mahmoud-elghamry/thermocouple/docs/reference/benchmarks/murphy-tdxm/photo-1.jpg

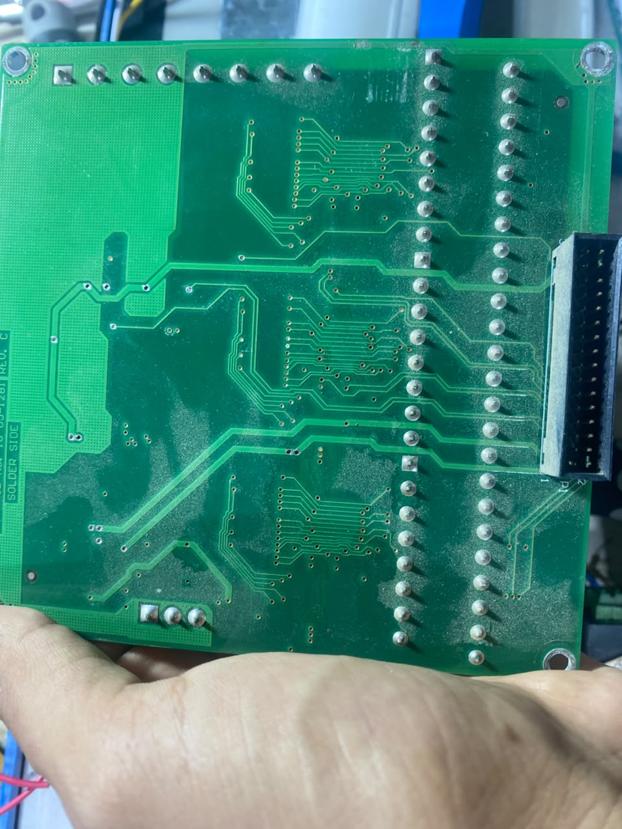
docs/reference/benchmarks/murphy-tdxm/photo-1.jpg
