mahmoud-elghamry/thermocouple/docs/reference/benchmarks/murphy-tdxm/photo-2.jpg

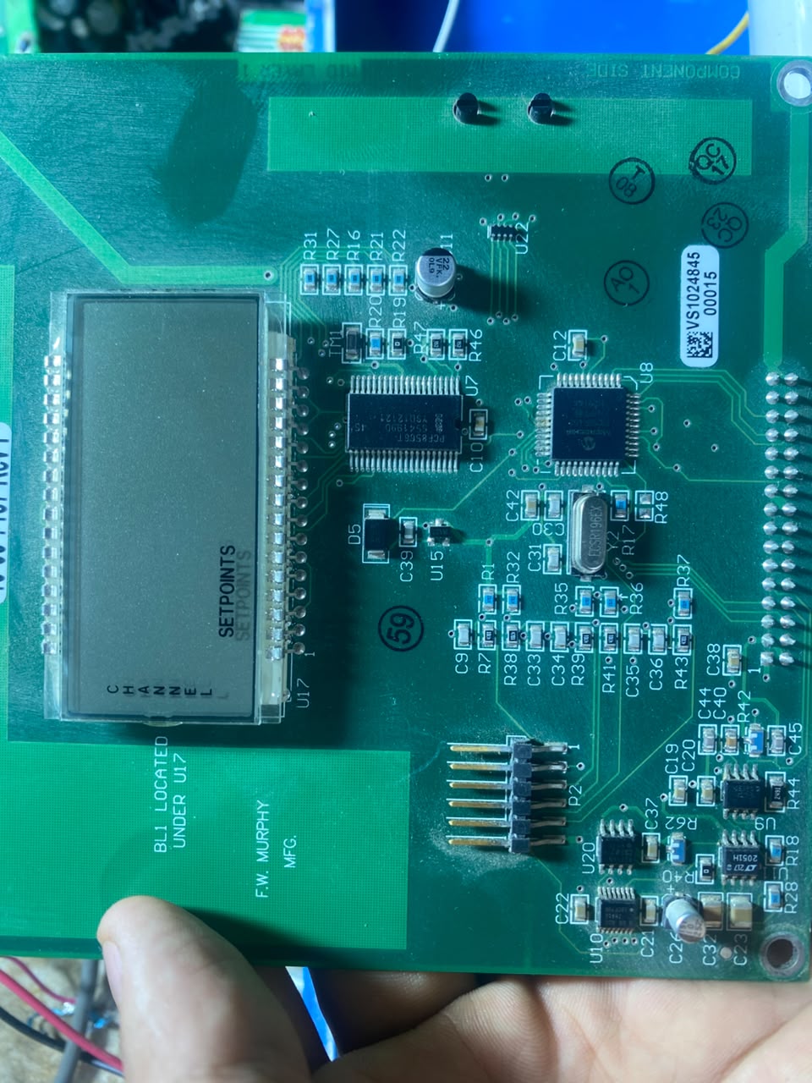
docs/reference/benchmarks/murphy-tdxm/photo-2.jpg
