mahmoud-elghamry/thermocouple/docs/reference/benchmarks/murphy-tdxm/photo-3.jpg

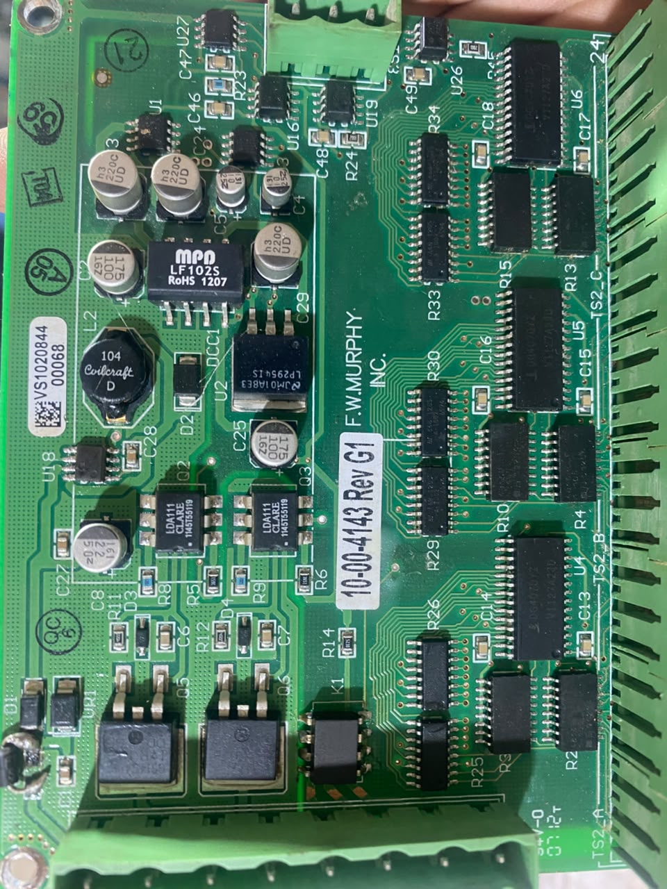
docs/reference/benchmarks/murphy-tdxm/photo-3.jpg
