mahmoud-elghamry/thermocouple/docs/reference/benchmarks/murphy-tdxm/photo-4.jpg

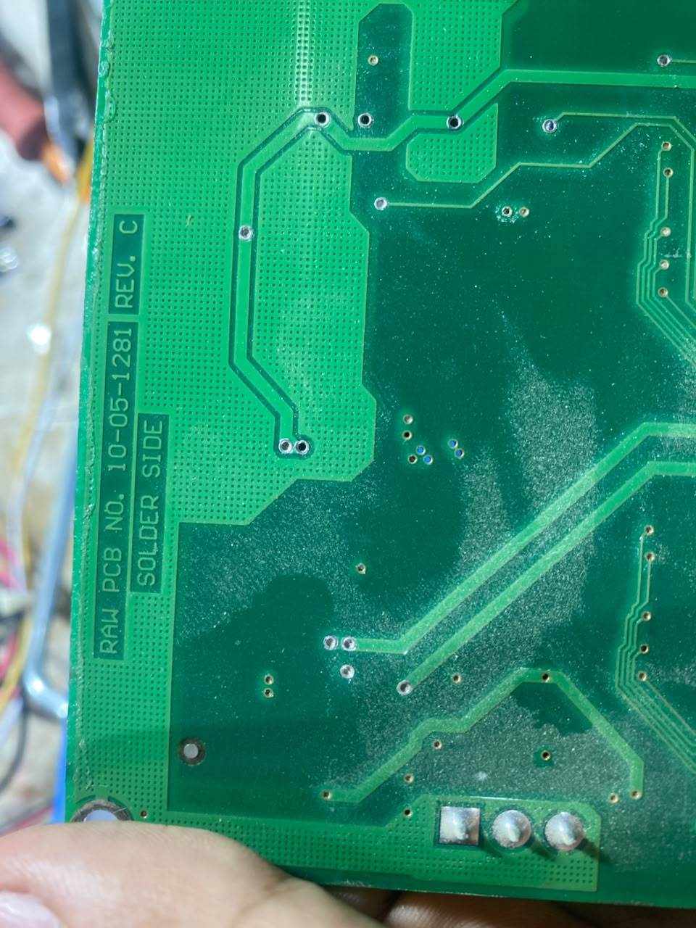
docs/reference/benchmarks/murphy-tdxm/photo-4.jpg
