mahmoud-elghamry/thermocouple/docs/reference/benchmarks/murphy-tdxm/photo-5.jpg

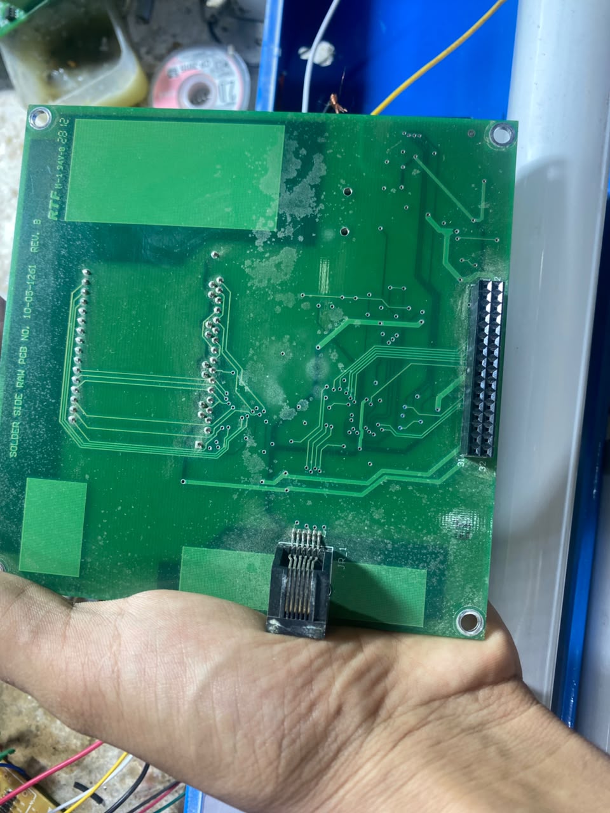
docs/reference/benchmarks/murphy-tdxm/photo-5.jpg
