mahmoud-elghamry/thermocouple/docs/reference/benchmarks/murphy-tdxm/photo-8.jpg

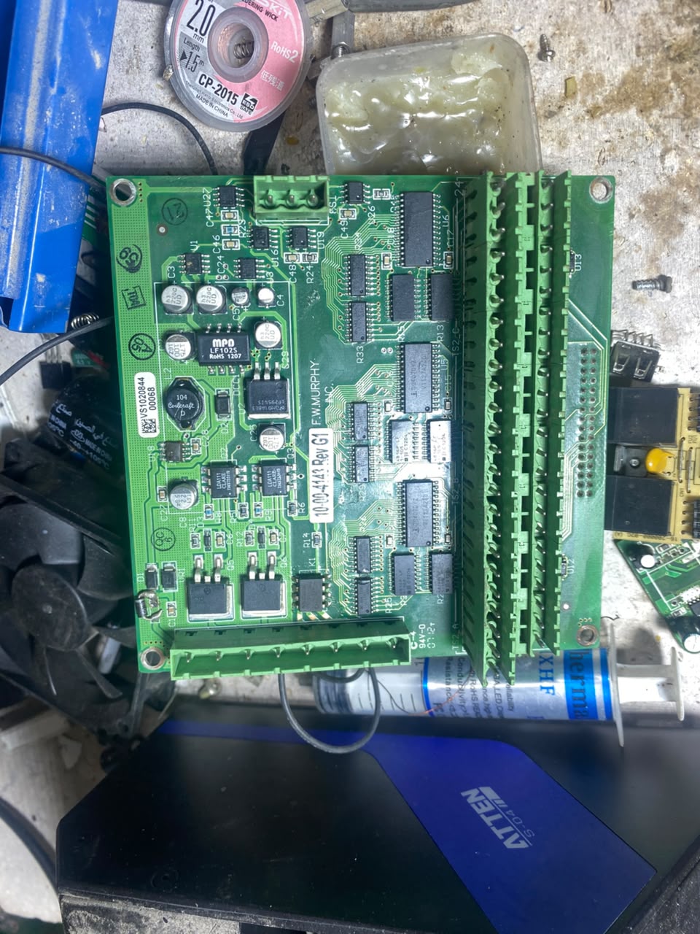
docs/reference/benchmarks/murphy-tdxm/photo-8.jpg
