mahmoud-elghamry/thermocouple/hardware/24ch/gen/finish.py

"""Incremental finishing of the routed board - never moves a footprint.

Works on ../thermo24.kicad_pcb after a routing result was kept (docs/TOOLS.md,
"24-channel board"). Run with KiCad's python:
    python finish.py drc                 # KiCad DRC -> ../output/finish-drc.json, prints a summary
    python finish.py stubs               # join pads to the via of their own net next to them
    python finish.py strip NET [NET...]  # delete the tracks and vias of these nets (to re-route them)
    python finish.py lock | unlock       # lock every track and via (the router keeps them, but
                                         # cannot shove them either - a fully locked run stalled)
    python finish.py unlock-box x1 y1 x2 y2 [...]   # free only the tracks inside the boxes
    python finish.py add NET LAYER W x1,y1 x2,y2 [...] [via]   # a hand route: track chain, optional via at the end
    python finish.py dangling            # delete dangling track/via stubs (DRC warnings)
    python finish.py nori                # push tracks off pads to the NORI pad-to-track minimum (from the DRC report)
    python finish.py dedupe              # delete exact duplicate segments and same-net vias whose holes overlap
"""
import json
import math
import os
import re
import subprocess
import sys
from collections import Counter

import pcbnew

HERE = os.path.dirname(os.path.abspath(__file__))
HW = os.path.dirname(HERE)
BOARD = os.environ.get("THERMO24_BOARD", os.path.join(HW, "thermo24.kicad_pcb"))   # a copy while KiCad holds the board
REPORT = os.path.join(HW, "output", "finish-drc.json")
CLI = os.environ.get("KICAD_CLI", r"C:\Program Files\KiCad\10.0\bin\kicad-cli.exe")
mm = pcbnew.FromMM


def drc(quiet=False):
    subprocess.run([CLI, "pcb", "drc", "--format", "json", "--severity-error", "--refill-zones",
                    "-o", REPORT, BOARD], capture_output=True, text=True)
    d = json.load(open(REPORT, encoding="utf-8"))
    if not quiet:
        kinds = Counter()
        for v in d["violations"]:
            m = re.search(r"rule '([^']+)'", v["description"])
            kinds[m.group(1) if m else v["type"]] += 1
        print(f"DRC: {len(d['violations'])} violations {dict(kinds)}, "
              f"{len(d['unconnected_items'])} unconnected")
    return d


def stubs():
    """A pad and a via of the same net, closer than 3 mm, reported unconnected: add the track."""
    d = drc(quiet=True)
    b = pcbnew.LoadBoard(BOARD)
    vias = [t for t in b.GetTracks() if t.Type() == pcbnew.PCB_VIA_T]
    added = 0
    for item in d["unconnected_items"]:
        descs = [i["description"] for i in item["items"]]
        pos = [i["pos"] for i in item["items"]]
        if not any(s.startswith("Via") for s in descs):
            continue
        k = 0 if descs[0].startswith("Via") else 1
        vx, vy = pos[k]["x"], pos[k]["y"]
        px, py = pos[1 - k]["x"], pos[1 - k]["y"]
        if math.hypot(vx - px, vy - py) > 3.0 or "pad" not in descs[1 - k].lower():
            continue
        via = min(vias, key=lambda v: math.hypot(pcbnew.ToMM(v.GetPosition().x) - vx,
                                                 pcbnew.ToMM(v.GetPosition().y) - vy))
        t = pcbnew.PCB_TRACK(b)
        t.SetStart(pcbnew.VECTOR2I(mm(px), mm(py)))
        t.SetEnd(via.GetPosition())
        t.SetWidth(mm(0.3))
        t.SetLayer(pcbnew.B_Cu if "B.Cu" in descs[1 - k] else pcbnew.F_Cu)
        t.SetNet(via.GetNet())
        b.Add(t)
        added += 1
    pcbnew.SaveBoard(BOARD, b)
    print(f"stubs: {added} pad-to-via tracks added")


def strip(nets):
    b = pcbnew.LoadBoard(BOARD)
    gone = [t for t in b.GetTracks() if t.GetNetname().rsplit("/", 1)[-1] in nets]
    for t in gone:
        b.Remove(t)
    pcbnew.SaveBoard(BOARD, b)
    print(f"strip: removed {len(gone)} tracks/vias of {sorted(nets)}")


def unlock_box(boxes):
    """Lock everything, then unlock tracks/vias fully inside any box (x1,y1,x2,y2 mm),
    so a short router run may shove only there."""
    b = pcbnew.LoadBoard(BOARD)
    n = 0
    for t in b.GetTracks():
        bb = t.GetBoundingBox()
        x1, y1 = pcbnew.ToMM(bb.GetLeft()), pcbnew.ToMM(bb.GetTop())
        x2, y2 = pcbnew.ToMM(bb.GetRight()), pcbnew.ToMM(bb.GetBottom())
        inside = any(a <= x1 and x2 <= c and bq <= y1 and y2 <= d for a, bq, c, d in boxes)
        t.SetLocked(not inside)
        n += inside
    pcbnew.SaveBoard(BOARD, b)
    print(f"unlock-box: {n} tracks/vias free inside {boxes}, the rest locked")


def rip(path):
    """Delete the tracks whose UUIDs are listed in path (written by maze.py --ripup)."""
    want = {l.strip() for l in open(path, encoding="utf-8") if l.strip()}
    b = pcbnew.LoadBoard(BOARD)
    gone = [t for t in b.GetTracks() if t.m_Uuid.AsString() in want]
    for t in gone:
        b.Remove(t)
    pcbnew.SaveBoard(BOARD, b)
    os.remove(path)
    print(f"rip: removed {len(gone)} of {len(want)} listed tracks")


def lock(state=True):
    b = pcbnew.LoadBoard(BOARD)
    n = 0
    for t in b.GetTracks():
        if t.IsLocked() != state:
            t.SetLocked(state)
            n += 1
    pcbnew.SaveBoard(BOARD, b)
    print(f"{'lock' if state else 'unlock'}: {n} tracks/vias changed")


def _anchored(b, net_code, p):
    """True if point p sits on an own-net pad or via (moving it would break the joint)."""
    for t in b.GetTracks():
        if t.Type() == pcbnew.PCB_VIA_T and t.GetNetCode() == net_code and t.HitTest(p, 0):
            return True
    for fp in b.GetFootprints():
        for pad in fp.Pads():
            if pad.GetNetCode() == net_code and pad.HitTest(p, 0):
                return True
    return False


def nori(margin=0.012):
    """Push tracks that pass a pad closer than the nori_pad_to_track rule asks (DRC report)
    sideways by the shortfall. Free segment ends drag the joined segments along; a segment
    pinned at one end swings about it. Re-run `drc` after; repeat until clean."""
    d = json.load(open(REPORT, encoding="utf-8"))
    b = pcbnew.LoadBoard(BOARD)
    tracks = {t.m_Uuid.AsString(): t for t in b.GetTracks()}
    pads = {p.m_Uuid.AsString(): p for fp in b.GetFootprints() for p in fp.Pads()}
    moved, skipped = 0, []
    for v in d["violations"]:
        if "nori_pad_to_track" not in v["description"]:
            continue
        want = float(re.search(r"clearance ([0-9.]+) mm", v["description"]).group(1))
        act = float(re.search(r"actual ([0-9.]+) mm", v["description"]).group(1))
        t = next((tracks.get(i["uuid"]) for i in v["items"] if i["uuid"] in tracks), None)
        p = next((pads.get(i["uuid"]) for i in v["items"] if i["uuid"] in pads), None)
        if t is None or p is None:
            skipped.append(v["description"][:40])
            continue
        s, e = t.GetStart(), t.GetEnd()
        sx, sy, ex, ey = (pcbnew.ToMM(c) for c in (s.x, s.y, e.x, e.y))
        L = math.hypot(ex - sx, ey - sy)
        if L < 1e-3:
            continue
        nx, ny = -(ey - sy) / L, (ex - sx) / L
        pp = p.GetPosition()
        px, py = pcbnew.ToMM(pp.x), pcbnew.ToMM(pp.y)
        # the point of the segment nearest the pad centre, and which side the pad is on
        k = max(0.0, min(1.0, ((px - sx) * (ex - sx) + (py - sy) * (ey - sy)) / (L * L)))
        if (px - (sx + k * (ex - sx))) * nx + (py - (sy + k * (ey - sy))) * ny > 0:
            nx, ny = -nx, -ny
        shift = want - act + margin
        fs, fe = not _anchored(b, t.GetNetCode(), s), not _anchored(b, t.GetNetCode(), e)
        if fs and fe:
            ds = de = shift
        elif fs and k < 0.9:
            ds, de = min(shift / max(1 - k, 0.1), 0.15), 0.0      # swing about the pinned end
        elif fe and k > 0.1:
            ds, de = 0.0, min(shift / max(k, 0.1), 0.15)
        else:
            skipped.append(f"{t.GetNetname()} near {p.GetParentFootprint().GetReference()}.{p.GetNumber()}")
            continue
        for old, dd in ((s, ds), (e, de)):
            if dd == 0.0:
                continue
            new = pcbnew.VECTOR2I(old.x + mm(nx * dd), old.y + mm(ny * dd))
            for o in b.GetTracks():     # drag every own-net segment ending here
                if o.Type() == pcbnew.PCB_VIA_T or o.GetNetCode() != t.GetNetCode():
                    continue
                if o.GetStart() == old:
                    o.SetStart(new)
                if o.GetEnd() == old:
                    o.SetEnd(new)
        moved += 1
    pcbnew.SaveBoard(BOARD, b)
    print(f"nori: {moved} tracks pushed, {len(skipped)} left for hand work: {skipped}")


def _copy_without(uuids, tag):
    """Temp copy of the board with these tracks/vias removed; returns its path stem.
    Runs in a child process: after a Remove, pcbnew cannot load another board."""
    tmp = os.path.join(HW, "output", "tmp-dangling")
    os.makedirs(tmp, exist_ok=True)
    stem = os.path.join(tmp, f"t{tag}")
    for ext in (".kicad_pro", ".kicad_dru"):
        src = os.path.splitext(BOARD)[0] + ext
        if os.path.exists(src):
            open(stem + ext, "wb").write(open(src, "rb").read())
    open(stem + ".txt", "w", encoding="utf-8").write(" ".join(uuids))
    subprocess.run([sys.executable, os.path.abspath(__file__), "_without", stem], check=True,
                   capture_output=True)
    return stem


def _without(stem):
    want = set(open(stem + ".txt", encoding="utf-8").read().split())
    b = pcbnew.LoadBoard(BOARD)
    for x in [x for x in b.GetTracks() if x.m_Uuid.AsString() in want]:
        b.Remove(x)
    pcbnew.SaveBoard(stem + ".kicad_pcb", b)


def _unconnected(stem):
    """KiCad DRC unconnected count of a temp copy (thread-safe: only runs kicad-cli)."""
    subprocess.run([CLI, "pcb", "drc", "--format", "json", "--severity-error", "--refill-zones", "-o", stem + ".json",
                    stem + ".kicad_pcb"], capture_output=True, text=True)
    return len(json.load(open(stem + ".json", encoding="utf-8"))["unconnected_items"])


def dangling():
    """Delete what KiCad DRC calls track_dangling / via_dangling (leftover router stubs).
    Each candidate is tried alone on a temp copy and deleted only if KiCad's unconnected
    count stays the same; repeats until DRC lists none that are safe to delete."""
    from concurrent.futures import ThreadPoolExecutor
    rep = os.path.join(HW, "output", "finish-warn.json")
    removed, kept = 0, set()
    for _ in range(6):
        subprocess.run([CLI, "pcb", "drc", "--format", "json", "--severity-warning", "--refill-zones",
                        "-o", rep, BOARD], capture_output=True, text=True)
        d = json.load(open(rep, encoding="utf-8"))
        uu = sorted({i["uuid"] for v in d["violations"] if v["type"] in ("track_dangling", "via_dangling")
                     for i in v["items"]} - kept)
        if not uu:
            break
        base = len(d["unconnected_items"])
        stems = [_copy_without({u}, i) for i, u in enumerate(uu)]
        with ThreadPoolExecutor(6) as ex:
            counts = list(ex.map(_unconnected, stems))
        safe = {u for u, c in zip(uu, counts) if c == base}
        kept |= set(uu) - safe
        if not safe:
            break
        if _unconnected(_copy_without(safe, "all")) != base:
            # as a set they break something; take the individually safe ones one at a time
            taken = set()
            for u in sorted(safe):
                if _unconnected(_copy_without(taken | {u}, "one")) == base:
                    taken.add(u)
            kept |= safe - taken
            if not taken:
                print("dangling: nothing more is safe to delete")
                break
            safe = taken
        stem = _copy_without(safe, "all")
        open(BOARD, "wb").write(open(stem + ".kicad_pcb", "rb").read())
        removed += len(safe)
    print(f"dangling: removed {removed} stub tracks/vias, kept {len(kept)} that carry a connection")


def dedupe():
    """Repeated maze/rip-up runs can leave the same segment twice, or a second via on top of a
    same-net via (DRC hole_to_hole). Keep the first of each; nothing else is touched."""
    b = pcbnew.LoadBoard(BOARD)
    seen, gone, vias = set(), [], []
    for t in b.GetTracks():
        if t.Type() == pcbnew.PCB_VIA_T:
            p = t.GetPosition()
            if any(v.GetNetCode() == t.GetNetCode() and (v.GetPosition() - p).EuclideanNorm() < mm(0.6)
                   for v in vias):
                gone.append(t)
            else:
                vias.append(t)
            continue
        k = (t.GetNetCode(), t.GetLayer(), t.GetWidth(),
             tuple(sorted([(t.GetStart().x, t.GetStart().y), (t.GetEnd().x, t.GetEnd().y)])))
        if k in seen:
            gone.append(t)
        seen.add(k)
    for t in gone:
        b.Remove(t)
    pcbnew.SaveBoard(BOARD, b)
    print(f"dedupe: removed {len(gone)} duplicate segments/vias")


def add(net, layer, width, pts, end_via):
    b = pcbnew.LoadBoard(BOARD)
    n = [v for k, v in b.GetNetsByName().items() if str(k).rsplit("/", 1)[-1] == net][0]
    lay = {"F.Cu": pcbnew.F_Cu, "B.Cu": pcbnew.B_Cu, "In2.Cu": pcbnew.In2_Cu}[layer]
    xy = [pcbnew.VECTOR2I(mm(float(a)), mm(float(c))) for a, c in (p.split(",") for p in pts)]
    for a, z in zip(xy, xy[1:]):
        t = pcbnew.PCB_TRACK(b)
        t.SetStart(a)
        t.SetEnd(z)
        t.SetWidth(mm(width))
        t.SetLayer(lay)
        t.SetNet(n)
        b.Add(t)
    if end_via:
        v = pcbnew.PCB_VIA(b)
        v.SetPosition(xy[-1])
        v.SetWidth(mm(0.6))
        v.SetDrill(mm(0.3))
        v.SetNet(n)
        b.Add(v)
    pcbnew.SaveBoard(BOARD, b)
    print(f"add: {len(xy) - 1} segments on {net}{' + via' if end_via else ''}")


def run(cmd):
    if cmd == "drc":
        drc()
    elif cmd == "stubs":
        stubs()
        drc()
    elif cmd == "strip":
        strip(set(sys.argv[2:]))
    elif cmd == "lock":
        lock()
    elif cmd == "unlock-box":
        vals = [float(v) for v in sys.argv[2:]]
        unlock_box([tuple(vals[i:i + 4]) for i in range(0, len(vals), 4)])
    elif cmd == "rip":
        rip(os.path.join(HW, "output", "maze-rip.txt"))
    elif cmd == "_without":
        _without(sys.argv[2])
    elif cmd == "dangling":
        dangling()
        drc()
    elif cmd == "nori":
        nori()
        drc()
    elif cmd == "dedupe":
        dedupe()
        drc()
    elif cmd == "unlock":
        lock(False)
    elif cmd == "add":
        args = sys.argv[2:]
        via = args[-1] == "via"
        add(args[0], args[1], float(args[2]), args[3:-1] if via else args[3:], via)
    else:
        raise SystemExit(__doc__)


if __name__ == "__main__":
    cmd = sys.argv[1] if len(sys.argv) > 1 else "drc"
    if cmd == "_without":                # child of `dangling`: writes a temp copy, parent holds the claim
        _without(sys.argv[2])
    else:
        import guard      # I-115: refuse while KiCad or another tool holds the board
        with guard.claim(BOARD, "finish.py"):
            run(cmd)
