mahmoud-elghamry/thermocouple/firmware/src/hal/temperature_max31856_bank.c

/* Eight MAX31856 converters on one SPI bus, one chip-select each.
 *
 * This is the driver for the eight-channel board (U2..U9).  It replaces the
 * MAX6675 bank, which only ever existed because Proteus has no MAX31856
 * model, and which left the real board with no firmware at all (I-030).
 *
 * Every channel carries its own configured/not-configured state.  A channel
 * that fails to answer is re-configured on the next scan instead of dragging
 * the whole bank down, and it reads as a fault while it is down, so the
 * protection layer latches rather than trusting a stale number.
 *
 * The relevant configuration registers are re-checked before every sample is
 * accepted, not only right after writing them, because a completed SPI
 * transfer does not mean the slave answered (I-038): AVR SPIF marks the
 * master's own clocking done, so a MISO line stuck at a fixed level after a
 * successful configure_channel() still reads as eight clean bytes forever.
 * This catches a stuck MISO and a converter whose registers drifted or reset
 * - including the averaging bits, which the read-back never checked before -
 * but it is not exhaustive: a stuck value that happens to still satisfy the
 * configuration masks would not be caught by it.
 */

#include "hal/temperature_bank.h"
#include "hal/tc_decode.h"
#include "mcal/board.h"
#include "mcal/gpio.h"
#include "mcal/spi.h"

#include <stddef.h>
#include <stdint.h>

/* Register map. */
#define REG_CR0    0x00u
#define REG_CR1    0x01u
#define REG_MASK   0x02u
#define REG_LTCBH  0x0Cu
#define REG_SR     0x0Fu
#define WRITE_BIT  0x80u

/* CR0: automatic conversion, 10 ms open-circuit test, 50 Hz rejection.
   The open-circuit test needs the total input resistance below 5 kOhm; the
   100 R series resistors plus 50 m of extension wire stay well under it. */
#define CR0_CMODE        0x80u
#define CR0_OCFAULT_10MS 0x10u
#define CR0_FILTER_50HZ  0x01u
#define CR0_CONFIG_MASK  0xB1u
#define CR0_STOP_CONFIG  (CR0_OCFAULT_10MS | CR0_FILTER_50HZ)
#define CR0_RUN_CONFIG   (CR0_CMODE | CR0_STOP_CONFIG)

/* CR1: K type, no averaging.  Averaging would multiply the conversion time
   and eat into the 1 s trip budget for no accuracy this unit needs.
   Bits [6:4] are the averaging field and bits [3:0] the type - the read-back
   checks must cover both, or a converter that drifts into averaging still
   passes as configured (I-038). */
#define CR1_K_TYPE      0x03u
#define CR1_TYPE_MASK   0x0Fu
#define CR1_AVG_1SAMPLE 0x00u
#define CR1_AVG_MASK    0x70u
#define CR1_CONFIG_MASK (CR1_AVG_MASK | CR1_TYPE_MASK)
#define CR1_RUN_CONFIG  (CR1_AVG_1SAMPLE | CR1_K_TYPE)

/* Fault mask register: 0x00 unmasks every fault so the status register
   reports all of them.  FAULT and DRDY are unconnected on this board
   (docs/decisions/0004), so the status register is the only path. */
#define MASK_ALL_FAULTS 0x00u

static uint8_t configured;   /* one bit per channel */
/* Set when a channel's conversion was just (re)started.  Its very next
   result is still the pre-restart register image, not a real reading, so
   that one scan is reported as a fault instead of trusted (I-038). */
static uint8_t settling;

static void select_channel(uint8_t channel)
{
    mcal_gpio_write(&BOARD_SENSOR_CS_PINS[channel], false);
}

static void deselect_channel(uint8_t channel)
{
    mcal_gpio_write(&BOARD_SENSOR_CS_PINS[channel], true);
}

static bool write_register(uint8_t channel, uint8_t address, uint8_t value)
{
    uint8_t received;
    bool ok;

    select_channel(channel);
    ok = mcal_spi_transfer((uint8_t)(address | WRITE_BIT), &received);
    ok = ok && mcal_spi_transfer(value, &received);
    deselect_channel(channel);
    return ok;
}

static bool read_register(uint8_t channel, uint8_t address, uint8_t *value)
{
    uint8_t received;
    bool ok;

    select_channel(channel);
    ok = mcal_spi_transfer(address, &received);
    ok = ok && mcal_spi_transfer(0x00u, value);
    deselect_channel(channel);
    return ok;
}

/* LTCBH, LTCBM, LTCBL and SR in one burst.  The MAX31856 auto-increments,
   and SR follows the temperature registers, so one transaction gives both
   the reading and the fault flags that qualify it. */
static bool read_sample_bytes(uint8_t channel, uint8_t data[4])
{
    uint8_t received;
    uint8_t index;
    bool ok;

    select_channel(channel);
    ok = mcal_spi_transfer(REG_LTCBH, &received);
    for (index = 0u; ok && index < 4u; ++index) {
        ok = mcal_spi_transfer(0x00u, &data[index]);
    }
    deselect_channel(channel);
    return ok;
}

/* Reads CR0 and CR1 back and checks them against what this driver always
 * configures.  This is the only defence against a converter that answers
 * every SPI transfer - so mcal_spi_transfer never times out - without the
 * bytes actually coming from the slave: AVR SPIF marks the master's own
 * clocking done, not that anything answered, so a MISO line stuck at a
 * fixed level after configure_channel() succeeded once still looks like a
 * completed transfer forever (I-038, I-014).  A MISO stuck at a level that
 * happens to still satisfy both masks - which excludes 0x00 and 0xFF, the
 * two failure modes actually seen - would not be caught by this check;
 * register read-back is not a substitute for verifying the physical bus.
 */
static bool configuration_ok(uint8_t channel)
{
    uint8_t cr0;
    uint8_t cr1;

    return read_register(channel, REG_CR0, &cr0) &&
           read_register(channel, REG_CR1, &cr1) &&
           (cr0 & CR0_CONFIG_MASK) == CR0_RUN_CONFIG &&
           (cr1 & CR1_CONFIG_MASK) == CR1_RUN_CONFIG;
}

/* Write the configuration while conversion is stopped, read it back, then
   start converting.  Reading it back is what turns a dead or mis-wired
   channel into a fault instead of a plausible number. */
static bool configure_channel(uint8_t channel)
{
    uint8_t cr0;
    uint8_t cr1;

    if (!write_register(channel, REG_CR0, CR0_STOP_CONFIG) ||
        !write_register(channel, REG_CR1, CR1_RUN_CONFIG) ||
        !write_register(channel, REG_MASK, MASK_ALL_FAULTS) ||
        !read_register(channel, REG_CR0, &cr0) ||
        !read_register(channel, REG_CR1, &cr1) ||
        (cr0 & CR0_CONFIG_MASK) != CR0_STOP_CONFIG ||
        (cr1 & CR1_CONFIG_MASK) != CR1_RUN_CONFIG ||
        !write_register(channel, REG_CR0, CR0_RUN_CONFIG) ||
        !configuration_ok(channel)) {
        return false;
    }
    return true;
}

static hal_temperature_sample_t invalid_sample(uint8_t faults)
{
    hal_temperature_sample_t sample;

    sample.temperature_x10 = 0;
    sample.faults = faults;
    sample.valid = false;
    return sample;
}

bool hal_temperature_bank_init(void)
{
    uint8_t channel;
    bool all_ok = true;

    /* Drive every chip-select high before any of them becomes an output, so
       no converter is selected while the bus is still undefined. */
    for (channel = 0u; channel < HAL_TEMPERATURE_BANK_CHANNELS; ++channel) {
        mcal_gpio_write(&BOARD_SENSOR_CS_PINS[channel], true);
    }
    for (channel = 0u; channel < HAL_TEMPERATURE_BANK_CHANNELS; ++channel) {
        mcal_gpio_output(&BOARD_SENSOR_CS_PINS[channel]);
    }

    /* MAX31856: data is latched on the falling edge and shifted out on the
       rising edge - SPI mode 1 (CPOL = 0, CPHA = 1). */
    mcal_spi_master_init(MCAL_SPI_MODE_1);

    configured = 0u;
    settling = 0u;
    for (channel = 0u; channel < HAL_TEMPERATURE_BANK_CHANNELS; ++channel) {
        if (configure_channel(channel)) {
            configured |= (uint8_t)(1u << channel);
            settling |= (uint8_t)(1u << channel);
        } else {
            all_ok = false;
        }
    }
    return all_ok;
}

hal_temperature_sample_t hal_temperature_bank_read(uint8_t channel)
{
    hal_temperature_sample_t sample;
    uint8_t data[4];
    uint8_t mask;

    if (channel >= HAL_TEMPERATURE_BANK_CHANNELS) {
        return invalid_sample(HAL_TEMPERATURE_FAULT_RANGE);
    }
    mask = (uint8_t)(1u << channel);

    /* A channel that lost the bus is re-configured here rather than in a
       separate recovery path, so there is exactly one place that can bring
       a converter back (I-014). */
    if ((configured & mask) == 0u) {
        if (!configure_channel(channel)) {
            return invalid_sample(HAL_TEMPERATURE_FAULT_INIT);
        }
        configured |= mask;
        /* The conversion this channel is about to report was still running,
           or had not even started, at the moment it was configured.  Skip
           exactly one scan so only this channel is delayed while it
           settles - the other seven are read normally in the same sweep
           (I-038).  Falls into the settling check below instead of
           returning here directly, so a channel that was already configured
           at boot and a channel recovered mid-scan both get exactly one
           invalid scan, not two. */
        settling |= mask;
    }

    if ((settling & mask) != 0u) {
        settling &= (uint8_t)~mask;
        return invalid_sample(HAL_TEMPERATURE_FAULT_INIT);
    }

    /* Re-validate every scan, not just once after writing it: a channel can
       drift out of configuration - or MISO can stick at a fixed level -
       without a single SPI transfer ever reporting failure (I-038). */
    if (!configuration_ok(channel)) {
        configured &= (uint8_t)~mask;
        return invalid_sample(HAL_TEMPERATURE_FAULT_INIT);
    }

    if (!read_sample_bytes(channel, data)) {
        configured &= (uint8_t)~mask;
        return invalid_sample(HAL_TEMPERATURE_FAULT_COMMUNICATION);
    }

    sample.temperature_x10 = tc_max31856_decode_x10(data);
    sample.faults = tc_max31856_fault_flags(data[3]);
    sample.valid = sample.faults == HAL_TEMPERATURE_FAULT_NONE;
    return sample;
}

const char *hal_temperature_bank_name(void)
{
    return "MAX31856";
}
