mahmoud-elghamry/thermocouple/firmware/src/hal/temperature_max6675.c

#include "hal/temperature_sensor.h"
#include "hal/tc_decode.h"
#include "mcal/board.h"
#include "mcal/gpio.h"
#include "mcal/spi.h"

#include <stdint.h>

/* See temperature_max6675_bank.c: mode 0 is the silicon, mode 1 is what the
   Proteus model needs, and the simulation target overrides it (I-018). */
#ifndef HAL_MAX6675_SPI_MODE
#define HAL_MAX6675_SPI_MODE MCAL_SPI_MODE_0
#endif

static bool max6675_read_frame(uint16_t *frame)
{
    uint8_t high;
    uint8_t low;
    bool ok;

    mcal_gpio_write(&BOARD_SENSOR_CS, false);
    ok = mcal_spi_transfer(0x00u, &high);
    ok = ok && mcal_spi_transfer(0x00u, &low);
    mcal_gpio_write(&BOARD_SENSOR_CS, true);

    if (!ok) {
        return false;
    }
    *frame = (uint16_t)((uint16_t)high << 8) | low;
    return true;
}

bool hal_temperature_sensor_init(void)
{
    mcal_gpio_write(&BOARD_SENSOR_CS, true);
    mcal_gpio_output(&BOARD_SENSOR_CS);
    mcal_spi_master_init(HAL_MAX6675_SPI_MODE);
    return true;
}

hal_temperature_sample_t hal_temperature_sensor_read(void)
{
    uint16_t frame;
    bool open;
    hal_temperature_sample_t sample;

    if (!max6675_read_frame(&frame)) {
        sample.temperature_x10 = 0;
        sample.faults = HAL_TEMPERATURE_FAULT_COMMUNICATION;
        sample.valid = false;
        return sample;
    }

    open = tc_max6675_frame_open(frame);
    sample.temperature_x10 = tc_max6675_decode_x10(frame);
    sample.faults = open ? HAL_TEMPERATURE_FAULT_OPEN
                         : HAL_TEMPERATURE_FAULT_NONE;
    sample.valid = !open;
    return sample;
}

const char *hal_temperature_sensor_name(void)
{
    return "MAX6675";
}
