mahmoud-elghamry/thermocouple/hardware/24ch/gen/sexp.py

"""Minimal S-expression reader/writer for KiCad files."""
import re

_TOK = re.compile(r'\s*(?:(\()|(\))|"((?:[^"\\]|\\.)*)"|([^\s()"]+))')


class Sym(str):
    """An unquoted atom."""


def parse(text):
    """Parse KiCad S-expression text into nested lists of Sym/str."""
    stack, cur, pos = [], [], 0
    n = len(text)
    while pos < n:
        m = _TOK.match(text, pos)
        if not m:
            if text[pos:].strip() == "":
                break
            raise ValueError(f"bad token at {pos}")
        pos = m.end()
        if m.group(1):
            stack.append(cur)
            cur = []
        elif m.group(2):
            done = cur
            cur = stack.pop()
            cur.append(done)
        elif m.group(3) is not None:
            cur.append(m.group(3).replace('\\"', '"').replace("\\\\", "\\"))
        else:
            cur.append(Sym(m.group(4)))
    return cur[0] if len(cur) == 1 else cur


def q(s):
    return '"' + str(s).replace("\\", "\\\\").replace('"', '\\"') + '"'


def fmt(v):
    if isinstance(v, int):
        return str(v)
    s = f"{v:.4f}".rstrip("0").rstrip(".")
    return "0" if s in ("-0", "") else s


def dump(node, indent=0):
    """Serialise nested lists back to KiCad-style text."""
    if not isinstance(node, list):
        if isinstance(node, Sym):
            return str(node)
        if isinstance(node, bool):
            return "yes" if node else "no"
        if isinstance(node, (int, float)):
            return fmt(node)
        return q(node)
    if not node:
        return "()"
    simple = all(not isinstance(x, list) for x in node)
    if simple and len(node) < 10:
        return "(" + " ".join(dump(x) for x in node) + ")"
    pad = "\t" * (indent + 1)
    out = "(" + dump(node[0])
    for x in node[1:]:
        if isinstance(x, list):
            out += "\n" + pad + dump(x, indent + 1)
        else:
            out += " " + dump(x)
    return out + "\n" + "\t" * indent + ")"


def find(node, key):
    """First child list whose head is key."""
    for x in node:
        if isinstance(x, list) and x and x[0] == key:
            return x
    return None


def findall(node, key):
    return [x for x in node if isinstance(x, list) and x and x[0] == key]
